maxbbraun/accent/server/assets/artwork/2001-bowman.gif

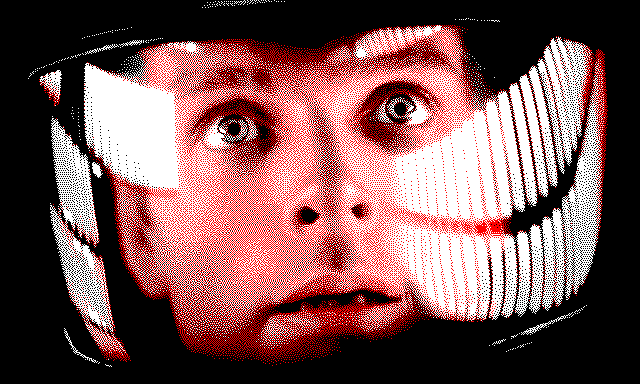
server/assets/artwork/2001-bowman.gif
