maxbbraun/accent/server/assets/artwork/eboy-san-francisco.gif

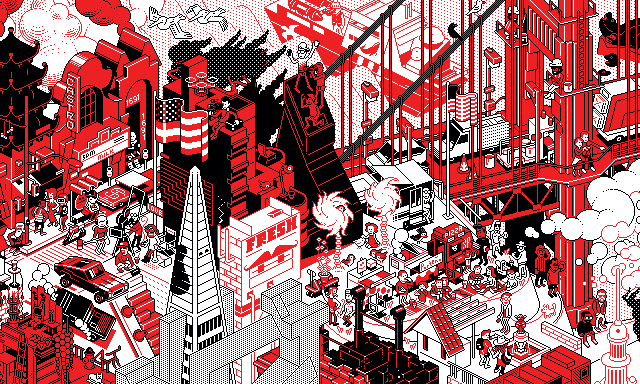
server/assets/artwork/eboy-san-francisco.gif
