maxbbraun/accent/server/assets/city/day/blocks/bldg-home-day.gif

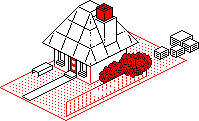
server/assets/city/day/blocks/bldg-home-day.gif
