maxbbraun/accent/server/assets/city/day/blocks/block-A/block-A-day-rain.gif

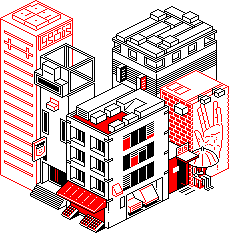
server/assets/city/day/blocks/block-A/block-A-day-rain.gif
