maxbbraun/accent/server/assets/city/day/blocks/block-C-day.gif

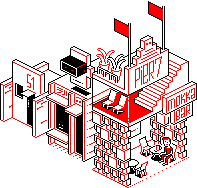
server/assets/city/day/blocks/block-C-day.gif
