maxbbraun/accent/server/assets/city/day/blocks/block-E/block-E-day-rain.gif

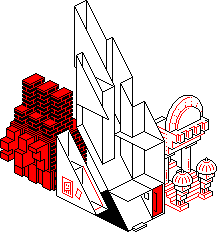
server/assets/city/day/blocks/block-E/block-E-day-rain.gif
