maxbbraun/accent/server/assets/city/day/environment/fog3-day.gif

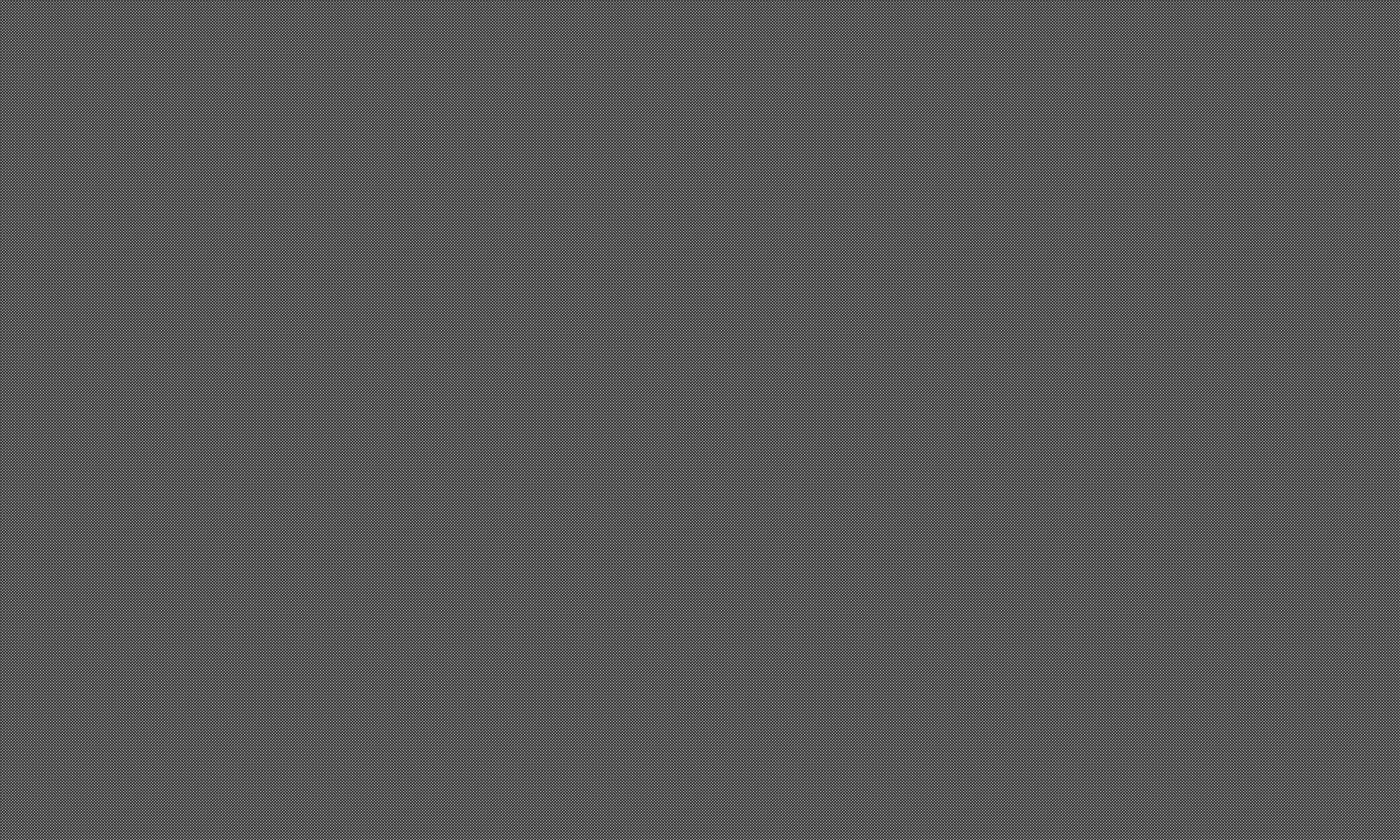
server/assets/city/day/environment/fog3-day.gif
