maxbbraun/accent/server/assets/city/day/environment/isle-day.gif

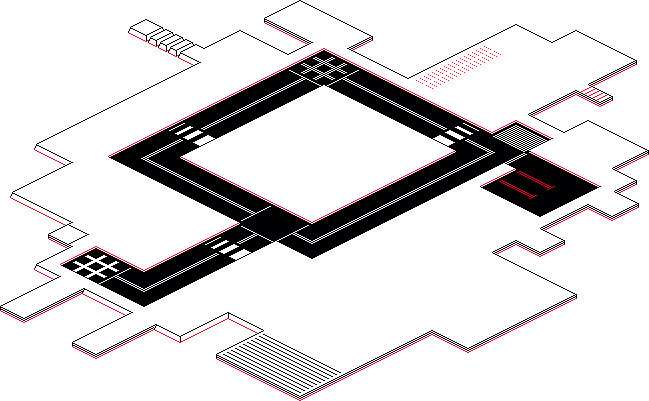
server/assets/city/day/environment/isle-day.gif
