maxbbraun/accent/server/assets/city/night/blocks/bldg-home-night.gif

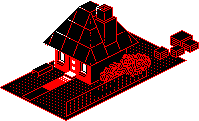
server/assets/city/night/blocks/bldg-home-night.gif
