maxbbraun/accent/server/assets/city/night/blocks/block-A/block-A-night-rain.gif

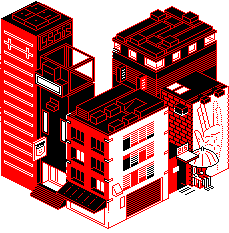
server/assets/city/night/blocks/block-A/block-A-night-rain.gif
