maxbbraun/accent/server/assets/city/night/blocks/block-C-night.gif

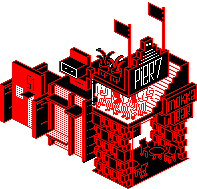
server/assets/city/night/blocks/block-C-night.gif
