maxbbraun/accent/server/assets/city/night/blocks/block-E-night.gif

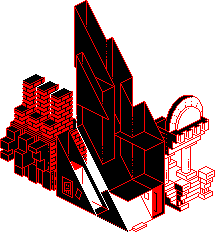
server/assets/city/night/blocks/block-E-night.gif
