maxbbraun/accent/server/assets/city/night/environment/isle-night.gif

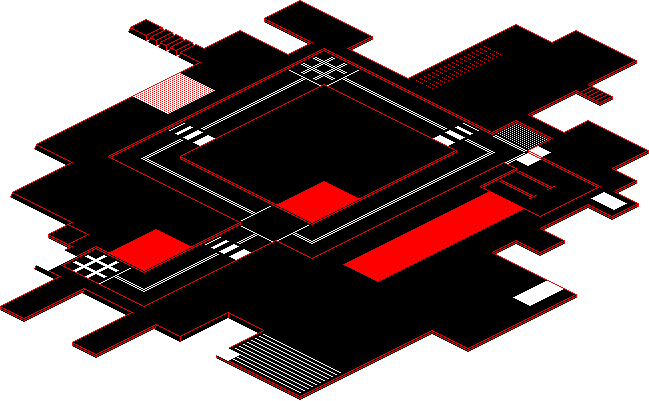
server/assets/city/night/environment/isle-night.gif
