maxbbraun/accent/server/assets/city/night/environment/rain1-night.gif

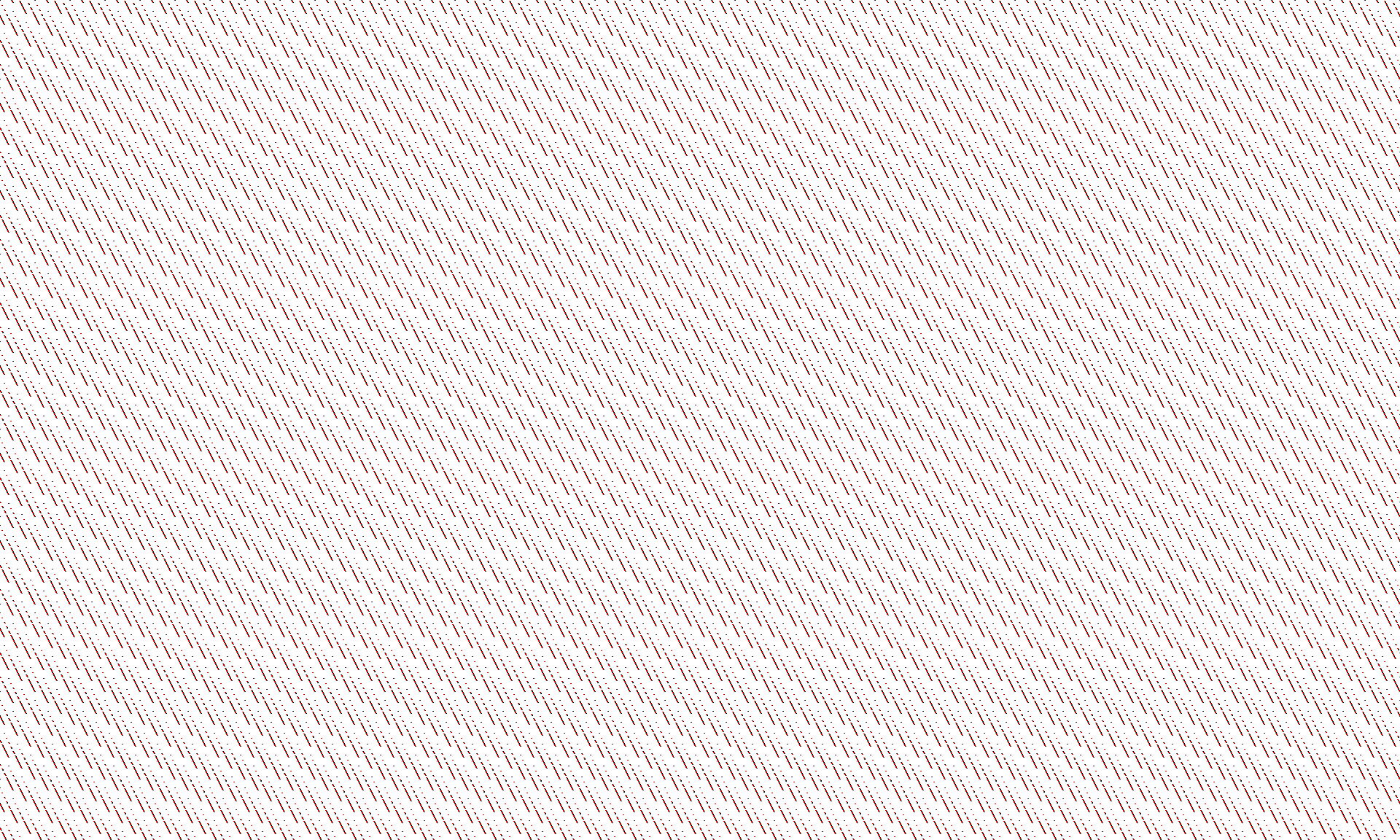
server/assets/city/night/environment/rain1-night.gif
