maxbbraun/accent/server/assets/city/night/environment/snow1-night.gif

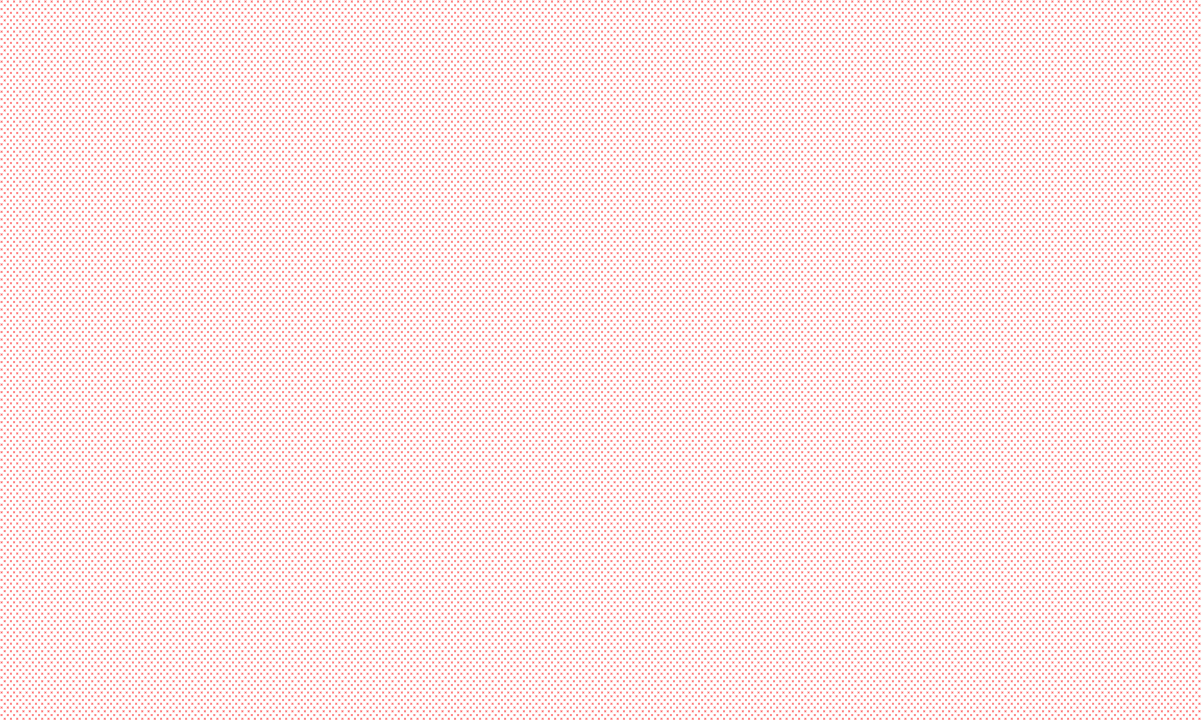
server/assets/city/night/environment/snow1-night.gif
