maxbbraun/accent/server/assets/client/wifi.gif

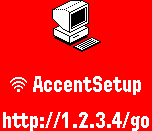
server/assets/client/wifi.gif
