maxbbraun/accent/client/include/WifiImage.h

#ifndef WIFI_IMAGE_H
#define WIFI_IMAGE_H

// Generated from "wifi.gif" using "client_image.py".
const uint16_t kWifiBackground = 0xF800;  // red
const uint16_t kWifiWidth = 152;
const uint16_t kWifiHeight = 131;
const PROGMEM uint8_t kWifiImageBlack[] =
    "\x00\x00\x00\x00\x00\x00\x00\x00\x03\xFF\xE0\x00\x00\x00\x00\x00\x00\x00"
    "\x00\x00\x00\x00\x00\x00\x00\x00\x00\x0C\x00\x98\x00\x00\x00\x00\x00\x00"
    "\x00\x00\x00\x00\x00\x00\x00\x00\x00\x00\x30\x02\x06\x00\x00\x00\x00\x00"
    "\x00\x00\x00\x00\x00\x00\x00\x00\x00\x00\x00\xC0\x08\x01\x80\x00\x00\x00"
    "\x00\x00\x00\x00\x00\x00\x00\x00\x00\x00\x00\x03\x00\x20\x06\x80\x00\x00"
    "\x00\x00\x00\x00\x00\x00\x00\x00\x00\x00\x00\x00\x0C\x00\x80\x18\x80\x00"
    "\x00\x00\x00\x00\x00\x00\x00\x00\x00\x00\x00\x00\x00\x30\x02\x00\x60\x80"
    "\x00\x00\x00\x00\x00\x00\x00\x00\x00\x00\x00\x00\x00\x00\xC0\x08\x01\x86"
    "\x80\x00\x00\x00\x00\x00\x00\x00\x00\x00\x00\x00\x00\x00\x03\x00\x20\x06"
    "\x1A\x80\x00\x00\x00\x00\x00\x00\x00\x00\x00\x00\x00\x00\x00\x0E\xAA\x80"
    "\x18\x7A\x80\x00\x00\x00\x00\x00\x00\x00\x00\x00\x00\x00\x00\x00\x08\x00"
    "\x20\x61\xFA\x80\x00\x00\x00\x00\x00\x00\x00\x00\x00\x00\x00\x00\x00\x08"
    "\x00\x09\x87\xFA\x80\x00\x00\x00\x00\x00\x00\x00\x00\x00\x00\x00\x00\x00"
    "\x08\x00\x06\x1F\xFA\x80\x00\x00\x00\x00\x00\x00\x00\x00\x00\x00\x00\x00"
    "\x00\x08\x00\x04\x7F\xFA\x80\x00\x00\x00\x00\x00\x00\x00\x00\x00\x00\x00"
    "\x00\x00\x08\x00\x05\xFF\xFA\x80\x00\x00\x00\x00\x00\x00\x00\x00\x00\x00"
    "\x00\x00\x00\x08\x00\x05\xFF\xFA\x80\x00\x00\x00\x00\x00\x00\x00\x00\x00"
    "\x00\x00\x00\x00\x08\x00\x05\xFF\xFA\x80\x00\x00\x00\x00\x00\x00\x00\x00"
    "\x00\x00\x00\x00\x00\x08\x00\x05\xFF\xFA\x80\x00\x00\x00\x00\x00\x00\x00"
    "\x00\x00\x00\x00\x00\x00\x08\x00\x05\xFF\xFA\x80\x00\x00\x00\x00\x00\x00"
    "\x00\x00\x00\x00\x00\x00\x00\x04\x00\x05\xFF\xFA\x80\x00\x00\x00\x00\x00"
    "\x00\x00\x00\x00\x00\x00\x00\x00\x02\x00\x05\xFF\xFA\x80\x00\x00\x00\x00"
    "\x00\x00\x00\x00\x00\x00\x00\x00\x00\x01\x00\x05\xFF\xE6\x80\x00\x00\x00"
    "\x00\x00\x00\x00\x00\x00\x00\x00\x00\x00\x00\x80\x05\xFF\x98\x80\x00\x00"
    "\x00\x00\x00\x00\x00\x00\x00\x00\x00\x00\x00\x00\x40\x05\xFE\x61\x80\x00"
    "\x00\x00\x00\x00\x00\x00\x00\x00\x00\x00\x00\x00\x00\x20\x05\xF9\x86\x00"
    "\x00\x00\x00\x00\x00\x00\x00\x00\x00\x00\x00\x00\x00\x00\x10\x05\xE6\x18"
    "\x00\x00\x00\x00\x00\x00\x00\x00\x00\x00\x00\x00\x00\x00\x00\x68\x05\x98"
    "\x66\x00\x00\x00\x00\x00\x00\x00\x00\x00\x00\x00\x00\x00\x00\x01\x84\x05"
    "\x61\x81\x80\x00\x00\x00\x00\x00\x00\x00\x00\x00\x00\x00\x00\x00\x06\x02"
    "\x05\x86\x06\x80\x00\x00\x00\x00\x00\x00\x00\x00\x00\x00\x00\x00\x00\x05"
    "\x81\x84\x18\x18\x80\x00\x00\x00\x00\x00\x00\x00\x00\x00\x00\x00\x00\x00"
    "\x04\x60\x64\x60\x60\x80\x00\x00\x00\x00\x00\x00\x00\x00\x00\x00\x00\x00"
    "\x00\x04\x18\x1D\x81\x80\x80\x00\x00\x00\x00\x00\x00\x00\x00\x00\x00\x00"
    "\x00\x00\x04\x06\x06\x06\x00\x80\x00\x00\x00\x00\x00\x00\x00\x00\x00\x00"
    "\x00\x00\x00\x04\x01\x80\x18\x00\x80\x00\x00\x00\x00\x00\x00\x00\x00\x00"
    "\x00\x00\x00\x00\x04\x00\x60\x60\x01\x80\x00\x00\x00\x00\x00\x00\x00\x00"
    "\x00\x00\x00\x00\x00\x06\x00\x19\x86\x06\x00\x00\x00\x00\x00\x00\x00\x00"
    "\x00\x00\x00\x00\x00\x00\x01\x80\x06\x18\x1F\x00\x00\x00\x00\x00\x00\x00"
    "\x00\x00\x00\x00\x00\x00\x00\x03\xE0\x04\x60\x7E\x18\x00\x00\x00\x00\x00"
    "\x00\x00\x00\x00\x00\x00\x00\x00\x01\xF8\x04\x01\xF8\x66\x00\x00\x00\x00"
    "\x00\x00\x00\x00\x00\x00\x00\x00\x00\x00\x7E\x04\x07\xE1\x91\x80\x00\x00"
    "\x00\x00\x00\x00\x00\x00\x00\x00\x00\x00\x00\x1F\x84\x1F\x86\x64\x60\x00"
    "\x00\x00\x00\x00\x00\x00\x00\x00\x00\x00\x00\x00\x07\xE4\x7E\x19\x99\x18"
    "\x00\x00\x00\x00\x00\x00\x00\x00\x00\x00\x00\x00\x00\x01\xFD\xF8\x66\x66"
    "\x78\x00\x00\x00\x00\x00\x00\x00\x00\x00\x00\x00\x00\x00\x00\x7F\xE1\x99"
    "\x99\xE0\x00\x00\x00\x00\x00\x00\x00\x00\x00\x00\x00\x00\x00\x00\x1F\x86"
    "\x66\x67\x80\x00\x00\x00\x00\x00\x00\x00\x00\x00\x00\x00\x00\x00\x00\x06"
    "\x19\x99\x9E\x00\x00\x00\x00\x00\x00\x00\x00\x00\x00\x00\x00\x00\x00\x00"
    "\x00\x62\x66\x78\x00\x00\x00\x00\x00\x00\x00\x00\x00\x00\x00\x00\x00\x00"
    "\x00\x00\x78\x99\xE0\x00\x00\x00\x00\x00\x00\x00\x00\x00\x00\x00\x00\x00"
    "\x00\x00\x00\x1E\x27\x80\x00\x00\x00\x00\x00\x00\x00\x00\x00\x00\x00\x00"
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
    "\xE0\x18\xE3\xC3\x80\x63\x18\x8F\xFF\xFF\xCF\x07\x9F\xC6\x38\x1E\x07\x81"
    "\xC0\x60\x18\xFF\x81\x80\x63\x18\x0F\xFF\xFF\xDC\x01\xDF\xC6\x30\x0C\x03"
    "\x00\xC0\x20\x18\x0F\x00\x80\x63\x18\x07\xFF\xFF\xF8\xF8\xFF\xC6\x31\x8C"
    "\x63\x18\xC6\x38\xFC\x07\x18\xE3\xE3\x18\xC7\xFF\xFF\xF3\xFE\x7F\xC6\x31"
    "\x8C\x63\x18\xC6\x38\xFE\x03\x18\xE3\xE3\x18\xC7\xFF\xFF\xF7\x8F\x7F\xC0"
    "\x31\xFC\x7F\x00\xC6\x38\xFF\xE3\x00\xE3\xE3\x18\xC7\xFF\xFF\xFE\x03\xFF"
    "\xC0\x31\xFC\x7F\x00\xC6\x38\xFF\xE3\x00\xE3\xE3\x18\xC7\xFF\xFF\xFC\xF9"
    "\xFF\x80\x11\x8C\x63\x1F\xC6\x38\xF8\xE3\x1F\xE3\xE3\x18\xC7\xFF\xFF\xFD"
    "\xFD\xFF\x8F\x11\x8C\x63\x1C\xC6\x38\xC8\xE3\x1C\xE3\x23\x18\xC7\xFF\xFF"
    "\xFF\x8F\xFF\x8F\x10\x0C\x03\x00\xC6\x38\x08\x03\x00\xE0\x20\x18\x07\xFF"
    "\xFF\xFF\x8F\xFF\x8F\x18\x1E\x07\x81\xC6\x3C\x1C\x07\x81\xF0\x70\x18\x0F"
    "\xFF\xFF\xFF\x8F\xFF\x8F\x1C\x3F\x0F\xC3\xC6\x3E\x3E\x0F\xC3\xF8\xF9\x18"
    "\x8F\xFF\xFF\xFF\xFF\xFF\xFF\xFF\xFF\xFF\xFF\xFF\xFF\xFF\xFF\xFF\xFF\xFF"
    "\xF8\xFF\xFF\xFF\xFF\xFF\xFF\xFF\xFF\xFF\xFF\xFF\xFF\xFF\xFF\xFF\xFF\xFF"
    "\xFF\xF8\xFF\xFF\xFF\xFF\xFF\xFF\xFF\xFF\xFF\xFF\xFF\xFF\xFF\xFF\xFF\xFF"
    "\xFF\xFF\xF8\xFF\xFF\xFF\xFF\xFF\xFF\xFF\xFF\xFF\xFF\xFF\xFF\xFF\xFF\xFF"
    "\xFF\xFF\xFF\xFF\xFF\xFF\xFF\xFF\xFF\xFF\xFF\xFF\xFF\xFF\xFF\xFF\xFF\xFF"
    "\xFF\xFF\xFF\xFF\xFF\xFF\xFF\xFF\xFF\xFF\xFF\xFF\xFF\xFF\xFF\xFF\xFF\xFF"
    "\xFF\xFF\xFF\xFF\xFF\xFF\xFF\xFF\xFF\xFF\xFF\xFF\xFF\xFF\xFF\xFF\xFF\xFF"
    "\xFF\xFF\xFF\xFF\xFF\xFF\xFF\xFF\xFF\xFF\xFF\xFF\xFF\xFF\xFF\xFF\xFF\xFF"
    "\xFF\xFF\xFF\xFF\xFF\xFF\xFF\xFF\xFF\xFF\xFF\xFF\xFF\xFF\xFF\xFF\xFF\xFF"
    "\xFF\xFF\xFF\xFF\xFF\xFF\xFF\xFF\xFF\xFF\xFF\xFF\xFF\xFF\xFF\xFF\xFF\xFF"
    "\xFF\xFF\xFF\xFF\xFF\xFF\xFF\xFF\xFF\xFF\xFF\xFF\xFF\xFF\xFF\xFF\xFF\xFF"
    "\xFF\xFF\xFF\xFF\xFF\xFF\xFF\xFF\xFF\xFF\xFF\xFF\xFF\xFF\xFF\xFF\xFF\xFF"
    "\xFF\xFF\xFF\xFF\xFF\xFF\xFF\xFF\xFF\xFF\xFF\xFF\xFF\xFF\xFF\xFF\xFF\xFF"
    "\xFF\xFF\xFF\xFF\xFF\xFF\xFF\xFF\xFF\xFF\xFF\xFF\xFF\xFF\xFF\xFF\xFF\xFF"
    "\xFF\xFF\xFF\xFF\xFF\xFF\xFF\xFF\xFF\xFF\xFF\xFF\xFF\xFF\xFF\xFF\xFF\xFF"
    "\xFF\xFF\xFF\xFF\xFF\xFF\xFF\xFF\xFF\xFF\xFF\xFF\xFF\xFF\xFF\xFF\xFF\xFF"
    "\xFF\xFF\xFF\xFF\xFF\xFF\xFF\xFF\xFF\xFF\xFF\xFF\xFF\xFF\xFF\xFF\xFF\xFF"
    "\xFF\xFF\xFF\xFF\xFF\xFF\xFF\xFF\xFF\xFF\xFF\xFF\xFF\xFF\xFF\xFF\xFF\xFF"
    "\xFF\xFF\xFF\xFF\xFF\xFF\xFF\xFF\xFF\xFF\xFF\xFF\xFF\xFF\xFF\xFF\xFF\xFF"
    "\xFF\xFF\xFF\xFF\xFF\xFF\xFF\xFF\xFF\xFF\xFF\xFF\xFF\xFF\xFF\xFF\xFF\xFF"
    "\xFF\xFF\xFF\xFF\xFF\xFF\xFF\xFF\xFF\xFF\xFF\xFF\xFF\xFF\xFF\xFF\xFF\xFF"
    "\xFF\xFF\xFF\xFF\xE3\xFF\xFF\xFF\xFF\xFF\xC7\xC7\x8F\xFF\x83\xFF\xC1\xFF"
    "\xF0\xFE\x3F\xFF\xFF\xE3\xFC\x7C\x7F\xFF\xFF\xCF\xCF\x0F\xFF\x01\xFF\x80"
    "\xFF\xF0\xFE\x7F\xFF\xFF\xE3\xFC\x7C\x7F\xFF\xFF\xCF\xCE\x0F\xFE\x00\xFF"
    "\x00\x7F\xE0\xFE\x7F\xFF\xFF\xE3\xFC\x7C\x7F\xFF\xFF\x8F\x8C\x0F\xFE\x38"
    "\xFF\x1C\x7F\xE0\xFC\x7F\xFF\xFF\xE2\x30\x00\x0C\x47\xFF\x9F\x9C\x0F\xFE"
    "\x30\xFF\x1C\x7F\xC0\xFC\xF9\x8E\x1F\xE0\x10\x00\x0C\x07\x0F\x9F\x9C\x8F"
    "\xFF\xF1\xFF\xFC\x7F\xC8\xFC\xF0\x0C\x0F\xE0\x10\x00\x0C\x03\x0F\x1F\x1D"
    "\x8F\xFF\xE1\xFF\xF0\xFF\x88\xF8\xE0\x18\x07\xE3\x1C\x7C\x7C\x63\x0F\x3F"
    "\x3F\x8F\xFF\xE3\xFF\xF1\xFF\x98\xF9\xE3\x18\xC7\xE3\x1C\x7C\x7C\x63\x0F"
    "\x3F\x3F\x8F\xFF\xC3\xFF\xF0\xFF\x18\xF9\xE3\x18\xC7\xE3\x1C\x7C\x7C\x63"
    "\xFE\x3E\x3F\x8F\xFF\xC7\xFF\xFC\x7F\x00\x31\xE3\x18\xC7\xE3\x1C\x7C\x7C"
    "\x63\xFE\x7E\x7F\x8F\xFF\x87\xFF\xFC\x7F\x00\x33\xE3\x18\xC7\xE3\x1C\x7C"
    "\x7C\x63\xFE\x7E\x7F\x8F\xFF\x8F\xFF\x1C\x7F\x00\x33\xE0\x18\xC7\xE3\x1C"
    "\x64\x64\x63\x0C\x7C\x7F\x8F\x87\x0F\xC3\x1C\x61\xF8\xE3\xF0\x18\xC7\xE3"
    "\x1C\x04\x04\x03\x0C\xFC\xFF\x8F\x87\x00\xC3\x00\x61\xF8\xE7\xF9\x18\x07"
    "\xE3\x1E\x0E\x0C\x07\x0C\xFC\xFF\x8F\x86\x00\xC3\x80\xE1\xF8\xE7\xFF\x1C"
    "\x0F\xE3\x1F\x1F\x1C\x47\x08\xF8\xFF\x8F\x86\x00\xC3\xC1\xE1\xF8\xC7\xFF"
    "\x1E\x1F\xFF\xFF\xFF\xFC\x7F\xFF\xFF\xFF\xFF\xFF\xFF\xFF\xFF\xFF\xFF\xFF"
    "\xF0\x1F\xFF\xFF\xFF\xFF\xFC\x7F\xFF\xFF\xFF\xFF\xFF\xFF\xFF\xFF\xFF\xFF"
    "\xFF\xF0\x3F\xFF\xFF\xFF\xFF\xFC\x7F\xFF\xFF\xFF\xFF\xFF\xFF\xFF\xFF\xFF"
    "\xFF\xFF\xF0\x7F\xFF";

#endif  // WIFI_IMAGE_H
