maxbbraun/accent/client/include/ErrorImage.h

#ifndef ERROR_IMAGE_H
#define ERROR_IMAGE_H

// Generated from "error.gif" using "client_image.py".
const uint16_t kErrorBackground = 0xF800;  // red
const uint16_t kErrorWidth = 40;
const uint16_t kErrorHeight = 85;
const PROGMEM uint8_t kErrorImageBlack[] =
    "\x00\x00\x00\x00\x00\x00\x1F\x00\x00\x00\x00\x3F\x80\x00\x00\x00\x3F\x80"
    "\x00\x00\x00\x7F\xC0\x00\x00\x00\x7F\xC0\x00\x00\x00\xFF\xE0\x00\x00\x00"
    "\xFF\xE0\x00\x00\x01\xFF\xF0\x00\x00\x01\x3F\xF0\x00\x00\x00\x1F\xF8\x00"
    "\x00\x07\xDF\xF8\x00\x00\x05\x5F\xFC\x00\x00\x00\x3F\xFC\x00\x00\x0A\x3F"
    "\xCE\x00\x00\x00\x3F\xF6\x00\x00\x20\x37\xF7\x00\x00\x1F\xDB\xCF\x00\x00"
    "\x2D\xAB\xFF\x80\x00\x5B\x6B\xFF\xE0\x00\x3F\xEB\xFF\xF8\x00\x1F\xEB\xFF"
    "\xFE\x00\x3F\xEB\xFF\xFF\x80\x5B\x6B\xFF\xFF\xE0\x2D\xAB\xFF\xFF\xF0\x1F"
    "\xDB\xFF\xFF\xF0\x20\x37\xFF\xFF\xF8\x1F\xFF\xFF\xFF\xF8\x00\x00\x3F\xFF"
    "\xF8\x0B\xFF\xFF\xFF\xF8\x0B\xFF\xFF\xFF\xF8\x0B\xFF\xFF\xFF\xF8\x0D\xFF"
    "\xFF\xEF\xF8\x0D\xDF\xDF\xEF\xF8\x0D\xFF\xFF\xEF\xF8\x0D\xFF\xFF\xEF\xF8"
    "\x0E\xFF\xFF\xEF\xF8\x0E\xFF\xFF\xEF\xF8\x0E\xFF\xFF\xEF\xF8\x0E\xFF\xFF"
    "\xEF\xF8\x0F\x7F\xFF\xEF\xF8\x0F\x7F\xFF\xEF\xF8\x0F\x7F\xFF\xEF\xF8\x0F"
    "\x7F\xFF\xEF\xF8\x0F\xBF\xFF\xEF\xF8\x0F\xBF\xFF\xEF\xF8\x1F\xBF\xFF\xEF"
    "\xF8\x1D\xBF\xFF\xDF\xF8\x1D\xDF\xFF\xBF\xF8\x1D\xDF\xFF\x7F\xF8\x0D\xDF"
    "\xFE\xFF\xF8\x0C\xDF\xFE\xFF\xF8\x07\x6F\xC6\xFF\xF0\x07\x6F\xC6\xEF\xF0"
    "\x00\x0F\xC6\xEF\xE0\x00\x0F\xC6\x0F\xE0\x00\x0F\xC6\xFF\xC0\x00\x0F\xC6"
    "\xFF\xC0\x00\x0F\xC7\x00\x00\x00\x1F\xC7\xE0\x00\x00\x7F\xC7\xE0\x00\x01"
    "\xFF\xCF\xE0\x00\x07\xFF\x3F\xE0\x00\x06\xDC\xFF\xE0\x00\x06\xDB\xFF\xE0"
    "\x00\x00\x03\x6F\xE0\x00\x00\x03\x6F\xE0\x00\x00\x00\x00\x00\x00\x00\x00"
    "\x00\x00\x00\x00\x00\x00\x00\x00\x00\x00\x00\x00\x00\x00\x00\x00\x00\x00"
    "\x00\x00\x00\x00\x00\x00\x00\x00\x00\x00\x00\x00\x00\x00\x00\x00\x00\x00"
    "\x00\x00\x00\x00\x00\x00\x00\x00\x00\x00\x00\x00\x00\x00\x00\x00\x00\x00"
    "\x00\x00\x00\x00\x00\x00\x00\x00\x00\x00\x00\x00\x00\x00\x00\x00\x00\x00"
    "\x00\x00\x00\x00\x00\x00\x00\x00\x00\x00\x00";
const PROGMEM uint8_t kErrorImageRed[] =
    "\xFF\xE0\xFF\xFF\xFF\xFF\xC0\x7F\xFF\xFF\xFF\x80\x3F\xFF\xFF\xFF\x80\x3F"
    "\xFF\xFF\xFF\x00\x1F\xFF\xFF\xFF\x00\x1F\xFF\xFF\xFE\x00\x0F\xFF\xFF\xFE"
    "\x00\x0F\xFF\xFF\xFC\x00\x07\xFF\xFF\xFA\xC0\x07\xFF\xFF\xF8\x20\x03\xFF"
    "\xFF\xF0\x00\x03\xFF\xFF\xF2\x80\x01\xFF\xFF\xE0\x00\x01\xFF\xFF\xC0\x00"
    "\x00\xFF\xFF\xC0\x00\x00\xFF\xFF\xDF\xC0\x00\x7F\xFF\xE0\x20\x00\x7F\xFF"
    "\xC0\x10\x00\x1F\xFF\x80\x10\x00\x07\xFF\xC0\x10\x00\x01\xFF\xE0\x10\x00"
    "\x00\x7F\xC0\x10\x00\x00\x1F\x80\x10\x00\x00\x0F\xC0\x10\x00\x00\x07\xE0"
    "\x20\x00\x00\x07\xDF\xC0\x00\x00\x03\xC0\x00\x00\x00\x03\xE0\x00\x00\x00"
    "\x03\xE0\x00\x00\x00\x03\xE0\x00\x00\x00\x03\xE0\x00\x00\x00\x03\xE0\x00"
    "\x00\x00\x03\xE0\x00\x00\x00\x03\xE0\x00\x00\x00\x03\xE0\x00\x00\x00\x03"
    "\xE0\x00\x00\x00\x03\xE0\x00\x00\x00\x03\xE0\x00\x00\x00\x03\xE0\x00\x00"
    "\x00\x03\xE0\x00\x00\x00\x03\xE0\x00\x00\x00\x03\xE0\x00\x00\x00\x03\xE0"
    "\x00\x00\x00\x03\xE0\x00\x00\x00\x03\xE0\x00\x00\x00\x03\xC0\x00\x00\x00"
    "\x03\xC0\x00\x00\x00\x03\xC0\x00\x00\x00\x03\xC0\x00\x00\x00\x03\xE0\x00"
    "\x00\x00\x03\xE0\x00\x00\x00\x03\xF0\x00\x00\x00\x07\xF0\x00\x10\x00\x07"
    "\xF8\x00\x10\x00\x0F\xFF\xE0\x10\x00\x0F\xFF\xE0\x10\x00\x1F\xFF\xE0\x10"
    "\x00\x1F\xFF\xE0\x10\x00\x3F\xFF\x80\x10\x0F\xFF\xFE\x00\x10\x0F\xFF\xF8"
    "\x00\x00\x0F\xFF\xF0\x00\x00\x0F\xFF\xF0\x00\x00\x0F\xFF\xF0\x00\x00\x0F"
    "\xFF\xF8\x00\x00\x0F\xFF\xFF\xF8\x00\x0F\xFF\xFF\xFC\x00\x1F\xFF\xFF\xFF"
    "\xFF\xFF\xFF\xFF\xFF\xFF\xFF\xFF\xFF\xFF\xFF\xFF\xFF\xFF\xFF\xFF\xFF\xFF"
    "\xFF\xFF\xFF\xFF\xFF\xFF\xFF\xFF\xFF\xFF\xFF\xFF\xFF\xFF\xFF\xFF\xFF\xFF"
    "\xFF\xFF\xE0\x83\x07\x0C\x1F\xE7\x99\x32\x64\xCF\xE7\x99\x32\x64\xCF\xE7"
    "\x99\x32\x64\xCF\xE0\x83\x06\x64\x1F\xE7\x93\x26\x64\x9F\xE7\x93\x26\x64"
    "\x9F\xE7\x99\x32\x64\xCF\xE0\x99\x33\x0C\xCF";

#endif  // ERROR_IMAGE_H
